TTNApeldoorn/aid-hittestress-2023/hardware/housing/PXL_20240218_104532205.jpg

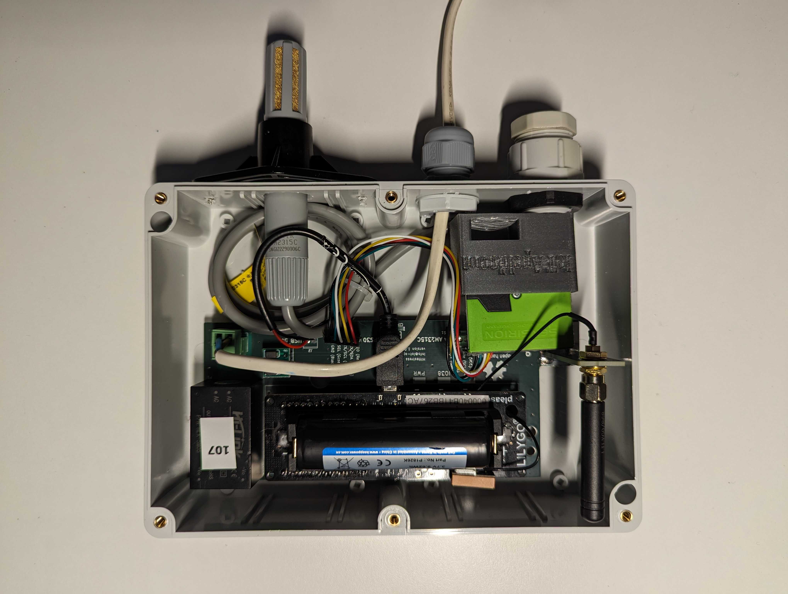
hardware/housing/PXL_20240218_104532205.jpg
